Loubear111/pic24_OLED_Clock/watch_State.h

/* 
 * File:   watch_State_header.h
 * Author: Bharath Muniraj
 *
 * Created on April 24, 2019, 9:35 PM
 */

#ifndef WATCH_STATE_H
#define	WATCH_STATE_H

#ifdef	__cplusplus
extern "C" {
#endif

    
void watch_setup(void);
int checkButton(int button); 
    
//extern int state;
//extern int edit; 
int watch_getState(void);
int watch_getEditState(void);
void watch_updateState(void); 
void watch_update(void);


#ifdef	__cplusplus
}
#endif

#endif	/* WATCH_STATE_HEADER_H */

//
